HackerspaceKRK/electronicJewelry/hsv.c

unsigned char hsvData[][3] = {
{ 255, 0, 0 },{ 255, 4, 0 },{ 255, 8, 0 },{ 255, 12, 0 },{ 255, 17, 0 },{ 255, 21, 0 },{ 255, 25, 0 },{ 255, 29, 0 },{ 255, 34, 0 },{ 255, 38, 0 },{ 255, 42, 0 },{ 255, 46, 0 },{ 255, 51, 0 },{ 255, 55, 0 },{ 255, 59, 0 },{ 255, 63, 0 },{ 255, 68, 0 },{ 255, 72, 0 },{ 255, 76, 0 },{ 255, 80, 0 },{ 255, 85, 0 },{ 255, 89, 0 },{ 255, 93, 0 },{ 255, 97, 0 },{ 255, 102, 0 },{ 255, 106, 0 },{ 255, 110, 0 },{ 255, 114, 0 },{ 255, 119, 0 },{ 255, 123, 0 },{ 255, 127, 0 },{ 255, 131, 0 },{ 255, 136, 0 },{ 255, 140, 0 },{ 255, 144, 0 },{ 255, 148, 0 },{ 255, 153, 0 },{ 255, 157, 0 },{ 255, 161, 0 },{ 255, 165, 0 },{ 255, 170, 0 },{ 255, 174, 0 },{ 255, 178, 0 },{ 255, 182, 0 },{ 255, 187, 0 },{ 255, 191, 0 },{ 255, 195, 0 },{ 255, 199, 0 },{ 255, 204, 0 },{ 255, 208, 0 },{ 255, 212, 0 },{ 255, 216, 0 },{ 255, 221, 0 },{ 255, 225, 0 },{ 255, 229, 0 },{ 255, 233, 0 },{ 255, 238, 0 },{ 255, 242, 0 },{ 255, 246, 0 },{ 255, 250, 0 },{ 255, 255, 0 },{ 250, 255, 0 },{ 246, 255, 0 },{ 242, 255, 0 },{ 237, 255, 0 },{ 233, 255, 0 },{ 229, 255, 0 },{ 225, 255, 0 },{ 221, 255, 0 },{ 216, 255, 0 },{ 212, 255, 0 },{ 208, 255, 0 },{ 203, 255, 0 },{ 199, 255, 0 },{ 195, 255, 0 },{ 191, 255, 0 },{ 187, 255, 0 },{ 182, 255, 0 },{ 178, 255, 0 },{ 174, 255, 0 },{ 169, 255, 0 },{ 165, 255, 0 },{ 161, 255, 0 },{ 157, 255, 0 },{ 153, 255, 0 },{ 148, 255, 0 },{ 144, 255, 0 },{ 140, 255, 0 },{ 135, 255, 0 },{ 131, 255, 0 },{ 127, 255, 0 },{ 123, 255, 0 },{ 119, 255, 0 },{ 114, 255, 0 },{ 110, 255, 0 },{ 106, 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
};
