HackerspaceKRK/electronicJewelry/arm-public/delay.h

#ifndef __DELAY_H__
#define __DELAY_H__

#include "public.h"

#include "settings.h"

#ifndef F_CPU
#	error F_CPU must be defined
#endif

// TIM2, TIM3, ...
#ifndef DELAY_TIMER
#	error DELAY_TIMER must be defined
#endif
// APB1ENR, ...
#ifndef DELAY_TIMER_APB
#	error DELAY_TIMER_APB must be defined
#endif
// APB1ENR_TIM2EN, ...
#ifndef DELAY_TIMER_APBEN
#	error DELAY_TIMER_APBEN must be defined
#endif

static inline void _delay_init ()
{
	RCC->DELAY_TIMER_APB |= DELAY_TIMER_APBEN;
}

#endif
